Balariash/R2B2/Model 3D/model_3D.png

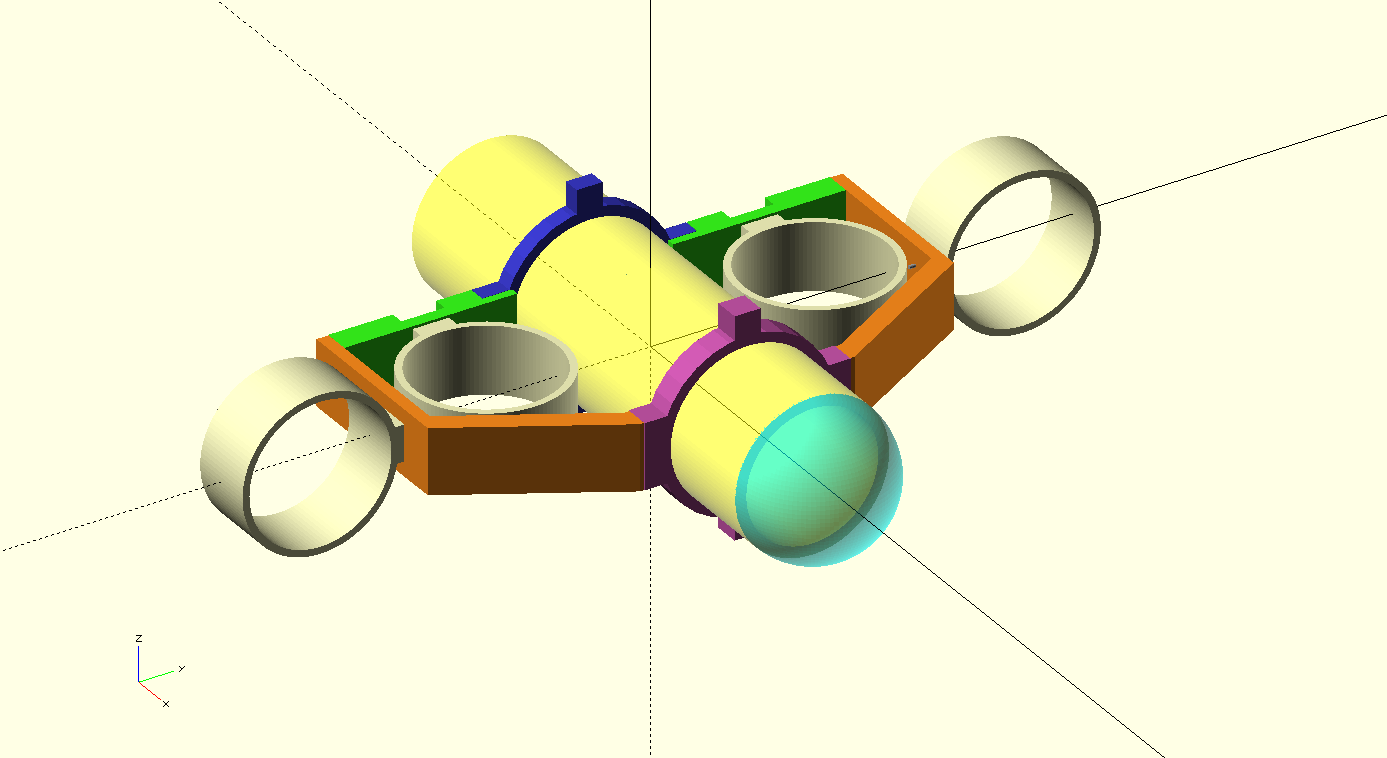
Model 3D/model_3D.png
