Balariash/R2B2/Model 3D/Peces/imatges/anell_davanter_v2.png

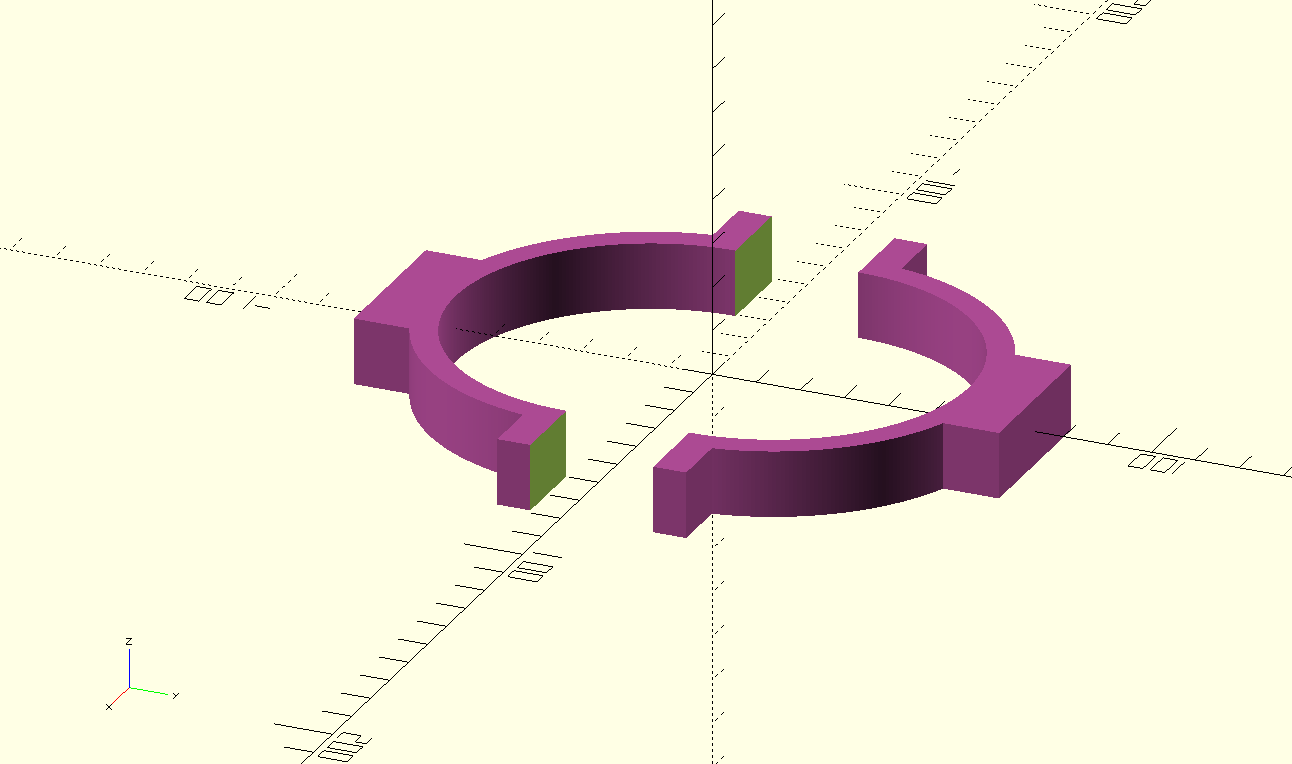
Model 3D/Peces/imatges/anell_davanter_v2.png
