Balariash/R2B2/Model 3D/Peces/imatges/suport_motor_vert.png

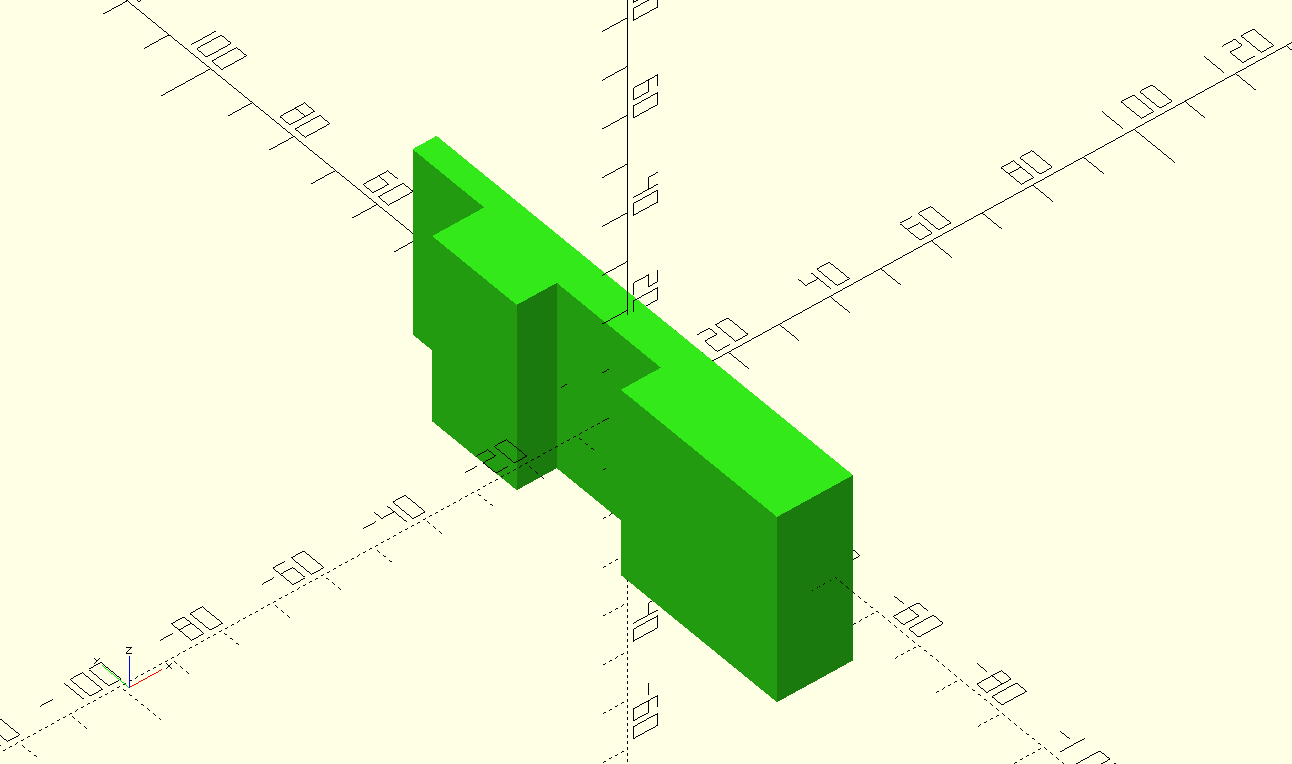
Model 3D/Peces/imatges/suport_motor_vert.png
