Balariash/R2B2/Model 3D/Suport intern/Peces per fressar/Imatges/barra_unio_3.png

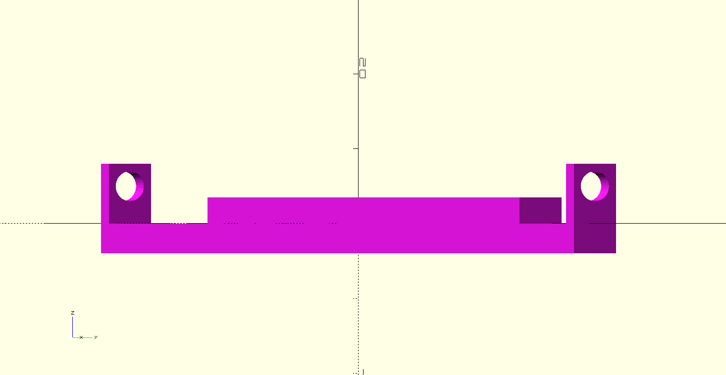
Model 3D/Suport intern/Peces per fressar/Imatges/barra_unio_3.png
