Balariash/R2B2/Model 3D/Suport intern/Peces per fressar/Imatges/estruct_intern_1.png

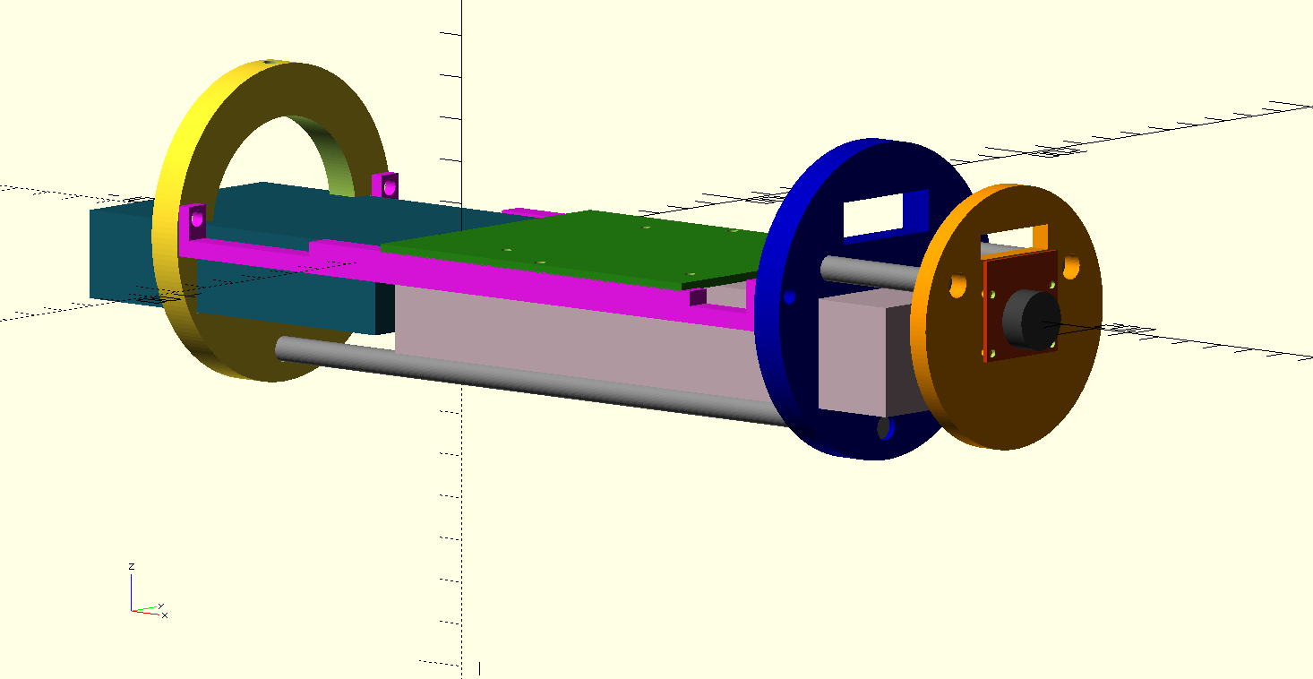
Model 3D/Suport intern/Peces per fressar/Imatges/estruct_intern_1.png
