Balariash/R2B2/Model 3D/Suport intern/Peces per fressar/Imatges/suport_bater_4.png

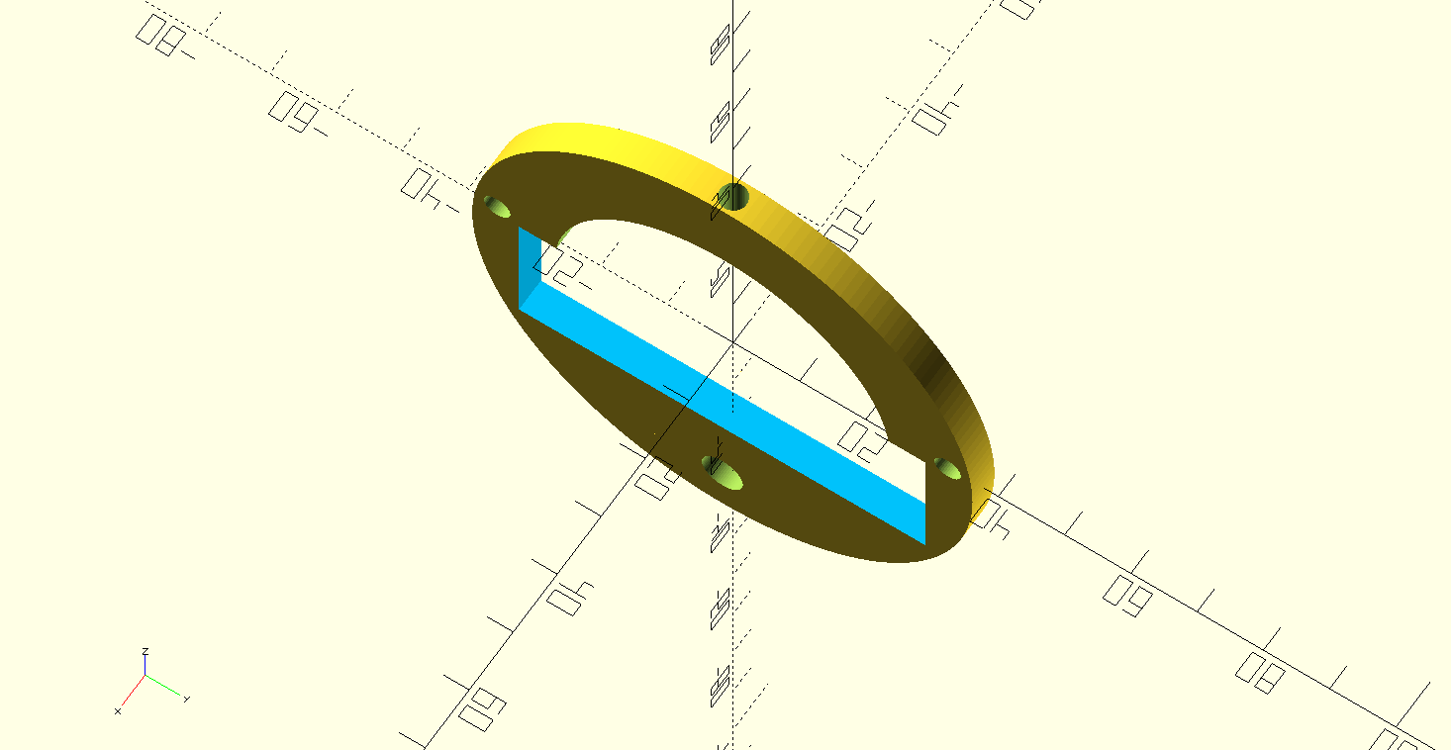
Model 3D/Suport intern/Peces per fressar/Imatges/suport_bater_4.png
