Balariash/R2B2/Model 3D/Suport intern/Peces per fressar/Imatges/suport_camera_2.png

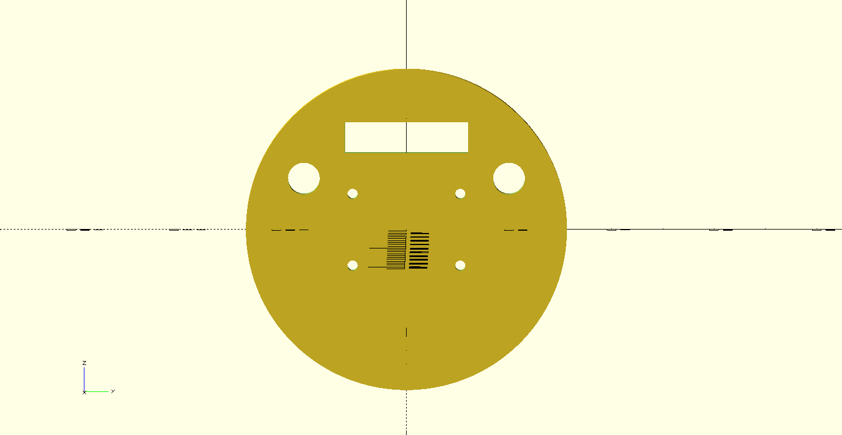
Model 3D/Suport intern/Peces per fressar/Imatges/suport_camera_2.png
