Balariash/R2B2/Model 3D/Peces/suport_motor_horitz.scad

/*
    Title  : Suport motor horitzontal
    Version: 1
    Author : Jordi Muñoz
    Data   : 23/11/2021
*/
include <../config/config.scad>
use <../model_3D.scad>

$fa = 1;
$fs = 0.3;

// Anell posterior
/*
projection() {
orange_chasis();}
*/
orange_chasis();
