Balariash/R2B2/Model 3D/Suport intern/barra_unio.scad

use <estruct_intern.scad>
include <config.scad>

projection() rotate([90,0,0]) barra(l=180, h=6);
