Balariash/R2B2/Model 3D/Suport intern/suport_bater.scad

use <estruct_intern.scad>
include <config.scad>

//projection() rotate([0,-90,0])suport_bater(h=h2, w=w2);

suport_bater(h=h2, w=w2);
