Balariash/R2B2/Model 3D/Suport intern/suport_camera.scad

use <estruct_intern.scad>
include <config.scad>

//projection() suport_camera();

rotate([0,90,0]) suport_camera();
