Balariash/R2B2/Model 3D/Suport intern/suport_lipo.scad

use <estruct_intern.scad>

//projection() rotate([0,90,0])suport_lipo();

suport_lipo();
