Balariash/R2B2/Model 3D/Suport intern/suport_raspi.scad

use <estruct_intern.scad>
include <config.scad>

suport_raspi();
