Balariash/R2B2/Model 3D/topes/barra.scad

use <topes.scad>

projection() barra();
