Balariash/R2B2/Model 3D/topes/tope_posterior.scad

use <topes.scad>


projection() rotate([0,0,0]) tope_posterior();
